autonabee/fit_and_fun/games/whattheduck/images/jewel_background.png

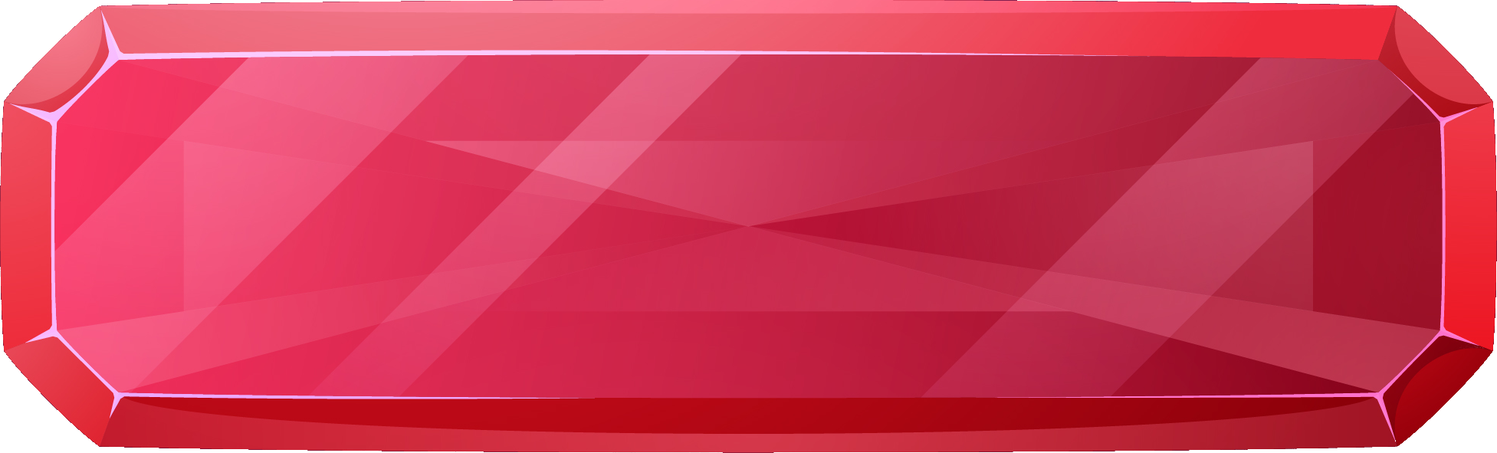
games/whattheduck/images/jewel_background.png
