autonabee/fit_and_fun/games/whattheduck/images/level_bg_landscape.png

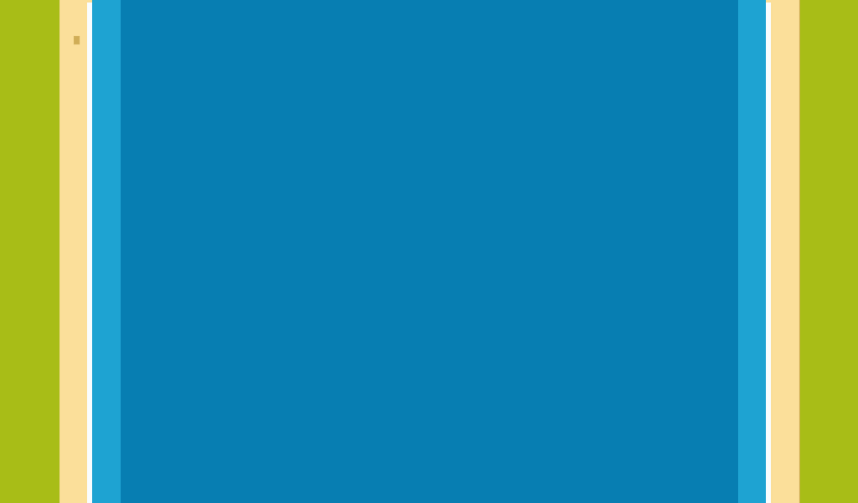
games/whattheduck/images/level_bg_landscape.png
