autonabee/fit_and_fun/games/whattheduck/images/level_bg_portrait.png

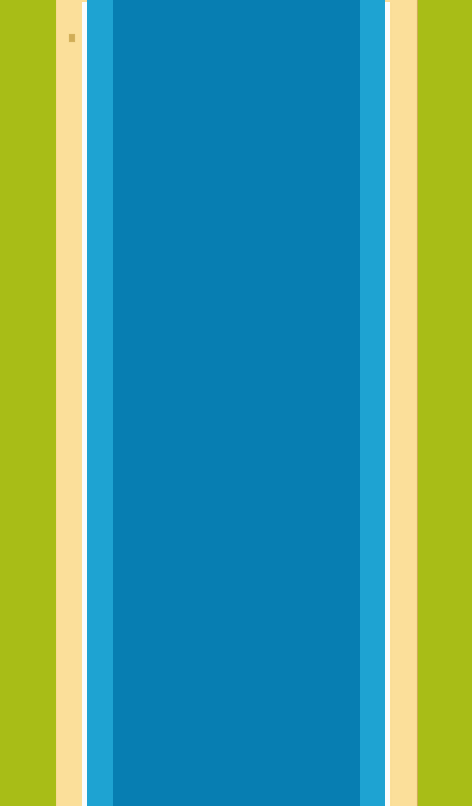
games/whattheduck/images/level_bg_portrait.png
