autonabee/fit_and_fun/games/whattheduck/images/level_bg_thick.png

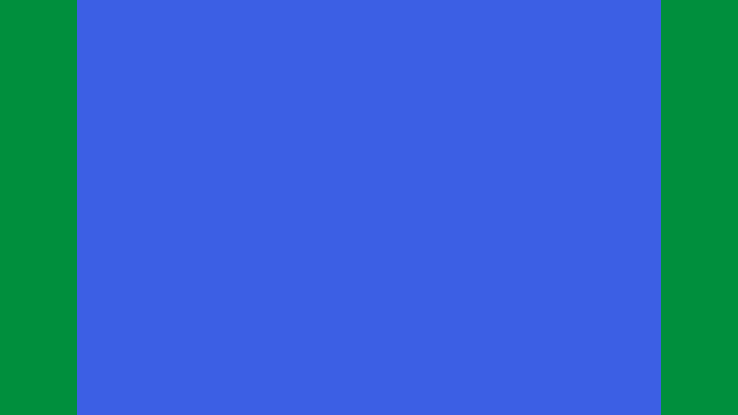
games/whattheduck/images/level_bg_thick.png
