autonabee/fit_and_fun/games/whattheduck/images/menu_bg_landscape.png

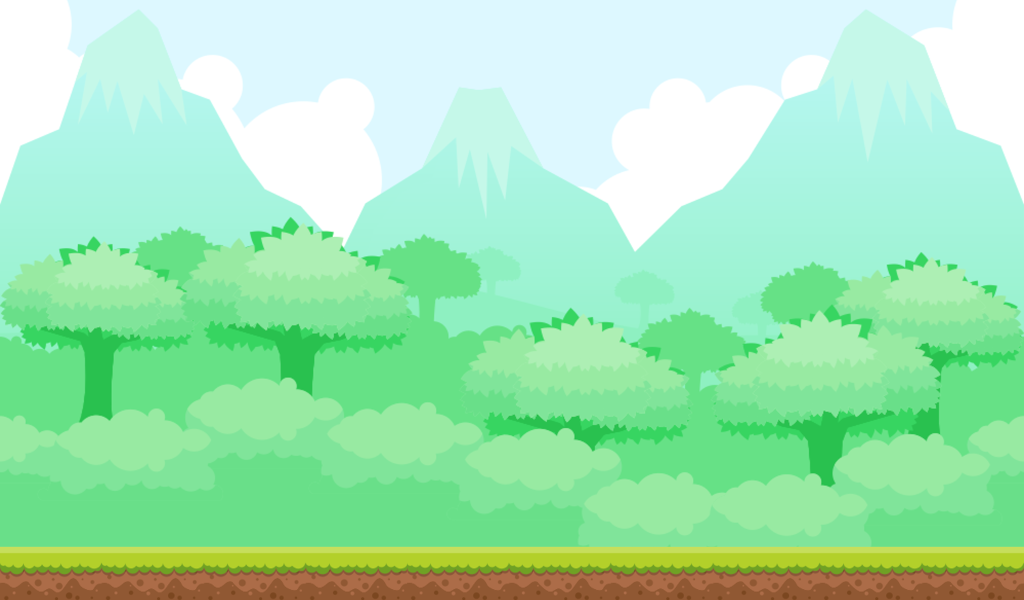
games/whattheduck/images/menu_bg_landscape.png
