autonabee/fit_and_fun/games/whattheduck/images/stone_background.png

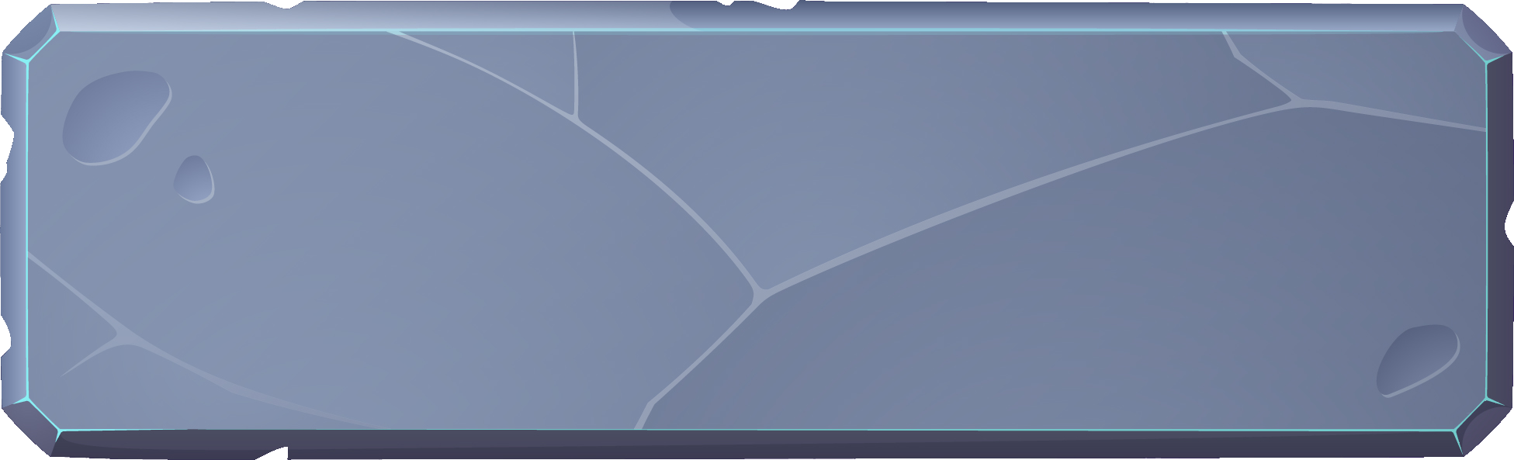
games/whattheduck/images/stone_background.png
