autonabee/fit_and_fun/games/whattheduck/images/wood_background.png

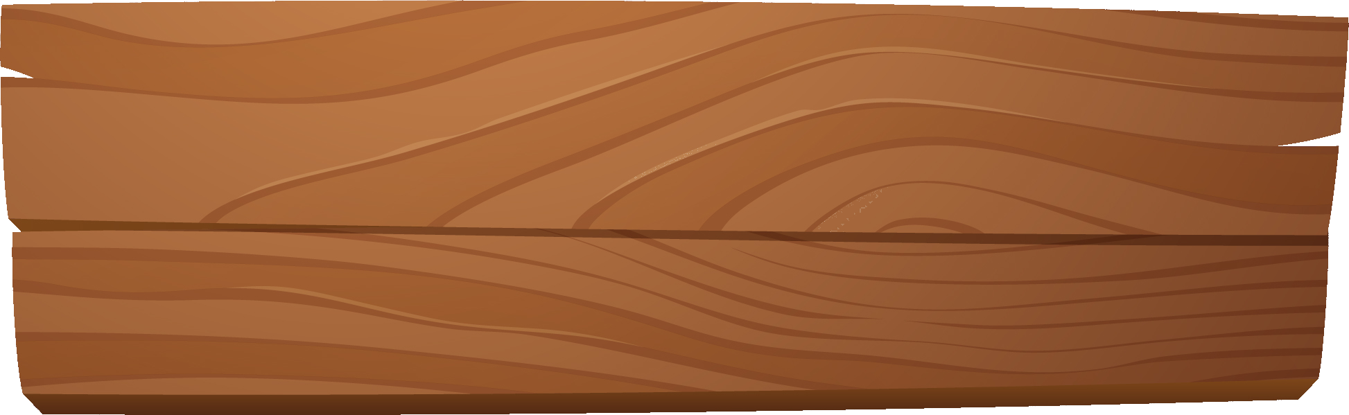
games/whattheduck/images/wood_background.png
